jakeyoshimoto/emg-robot-arm/CAD/v6/Index mcp v6.STL

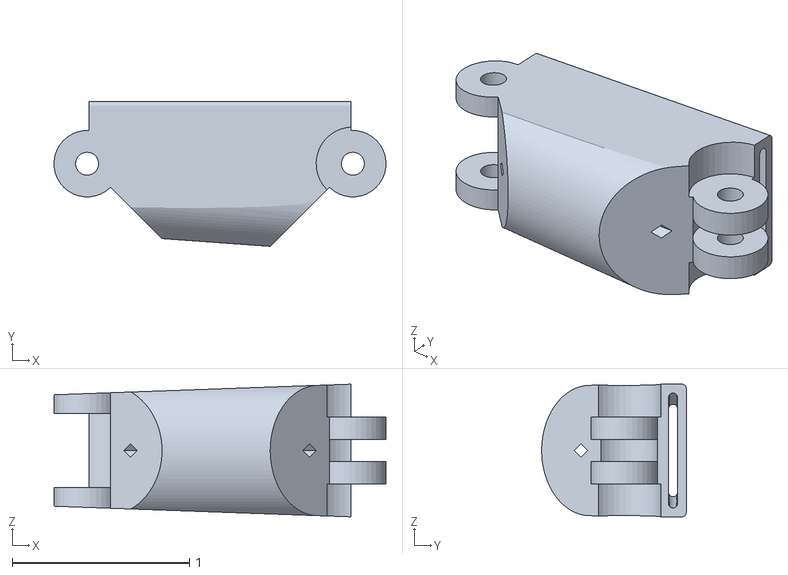
[picture p15: CAD file, 2026-07-24]
CAD/v6/Index mcp v6.STL
1.87 x 0.817 x 0.749
