jakeyoshimoto/emg-robot-arm/CAD/6DoF Arm/Arm 1.stl

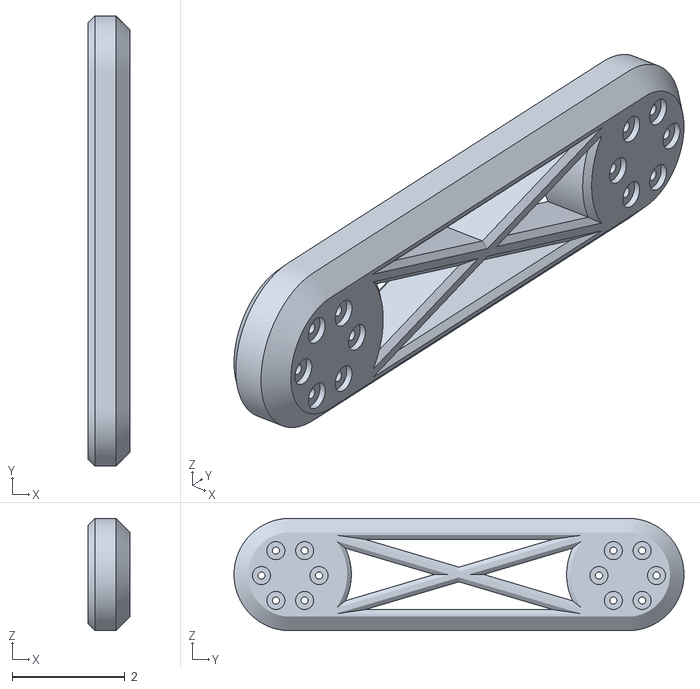
[picture p16: CAD file, 2026-07-29]
CAD/6DoF Arm/Arm 1.stl
0.75 x 8.00 x 2.00
