jakeyoshimoto/emg-robot-arm/CAD/Cycloidal Drive Gearbox/CDG V2 - Bottom Plate.stl

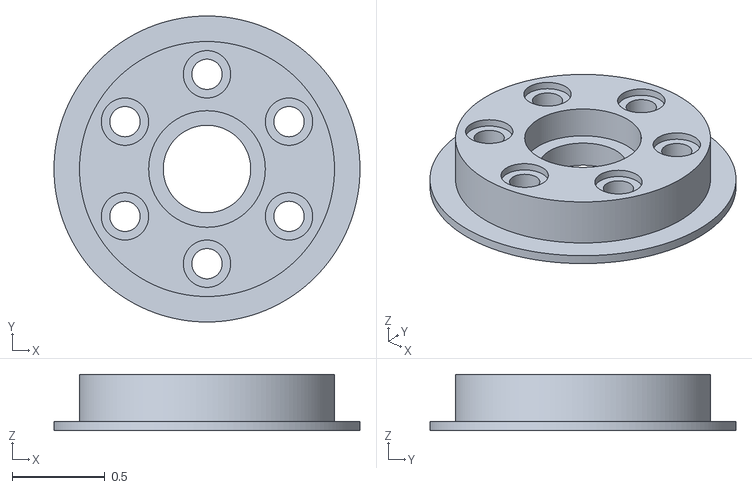
[picture p17: CAD file, 2026-07-28]
CAD/Cycloidal Drive Gearbox/CDG V2 - Bottom Plate.stl
1.65 x 1.65 x 0.305
