jakeyoshimoto/emg-robot-arm/CAD/v6/Middle_Ring dip v6.STL

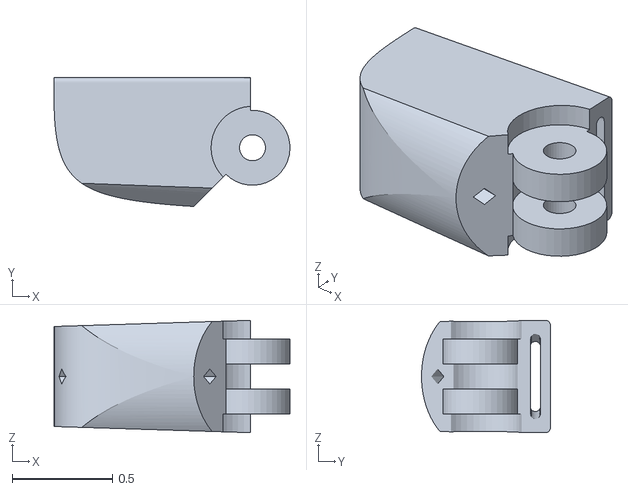
[picture p18: CAD file, 2026-07-24]
CAD/v6/Middle_Ring dip v6.STL
1.18 x 0.645 x 0.562
