jakeyoshimoto/emg-robot-arm/CAD/6DoF Arm/Arm 2.stl

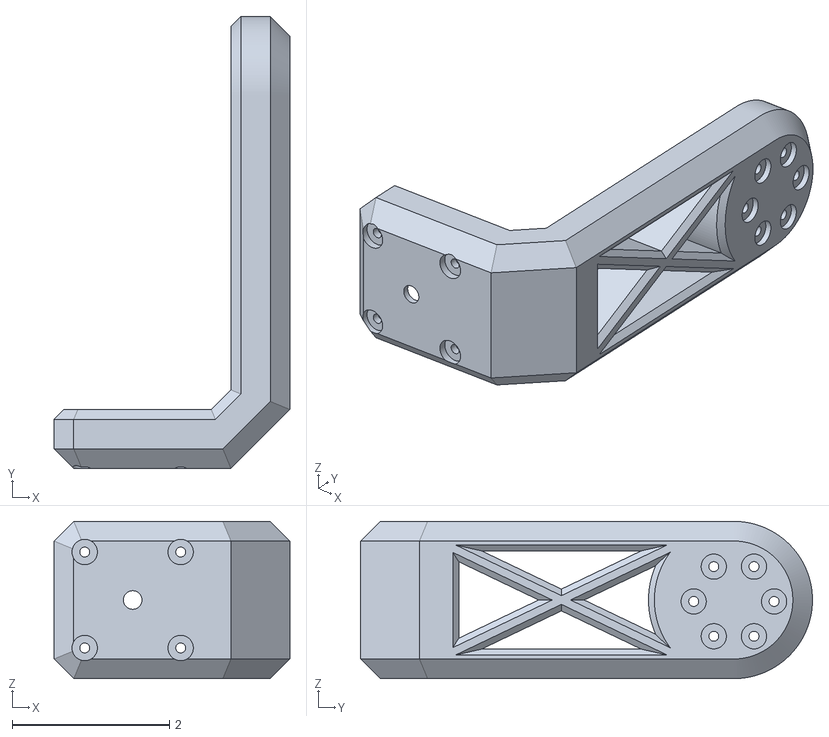
[picture p19: CAD file, 2026-07-29]
CAD/6DoF Arm/Arm 2.stl
3.00 x 5.75 x 2.00
