jakeyoshimoto/emg-robot-arm/CAD/v6/Middle_Ring pip v6.STL

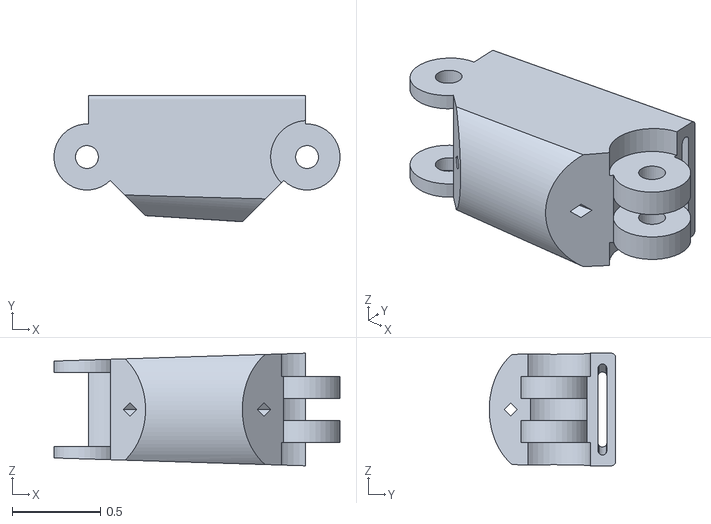
[picture p20: CAD file, 2026-07-24]
CAD/v6/Middle_Ring pip v6.STL
1.62 x 0.718 x 0.64
