jakeyoshimoto/emg-robot-arm/CAD/Cycloidal Drive Gearbox/CDG V2 - Top Plate.stl

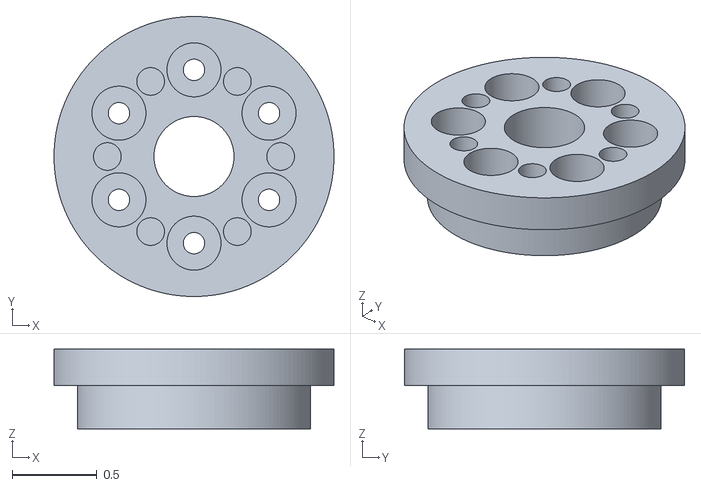
[picture p21: CAD file, 2026-07-28]
CAD/Cycloidal Drive Gearbox/CDG V2 - Top Plate.stl
1.65 x 1.65 x 0.472
