jakeyoshimoto/emg-robot-arm/CAD/v6/palm top no thumb v7.STL

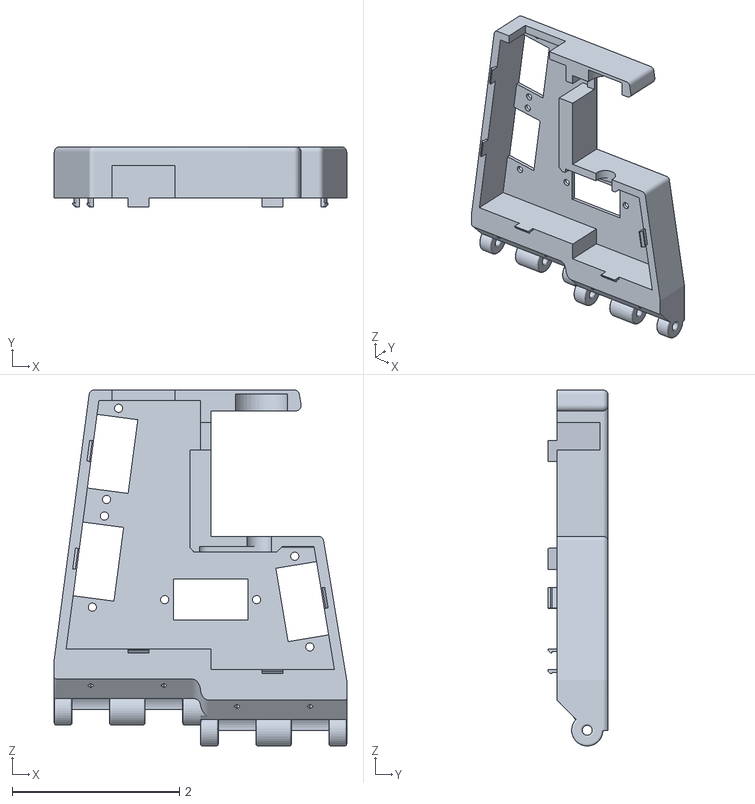
[picture p22: CAD file, 2026-07-24]
CAD/v6/palm top no thumb v7.STL
3.50 x 0.722 x 4.26
