jakeyoshimoto/emg-robot-arm/CAD/6DoF Arm/Hand Joint Mount.stl

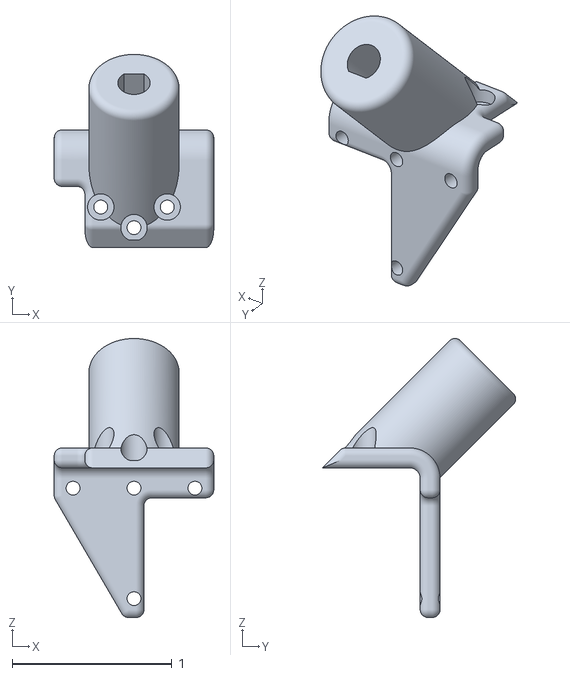
[picture p23: CAD file, 2026-07-29]
CAD/6DoF Arm/Hand Joint Mount.stl
1.00 x 1.21 x 1.75
