jakeyoshimoto/emg-robot-arm/CAD/Cycloidal Drive Gearbox/CDG V2 - Input Shaft T.stl

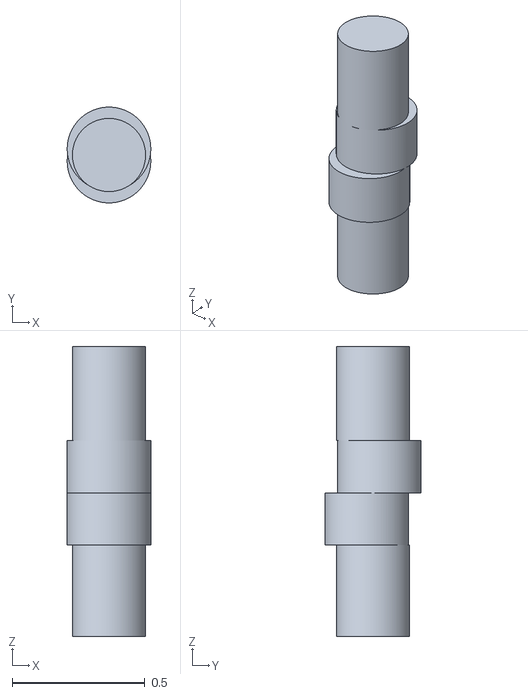
[picture p24: CAD file, 2026-07-28]
CAD/Cycloidal Drive Gearbox/CDG V2 - Input Shaft T.stl
0.315 x 0.361 x 1.09
