jakeyoshimoto/emg-robot-arm/CAD/v6/Pinky dip v6.STL

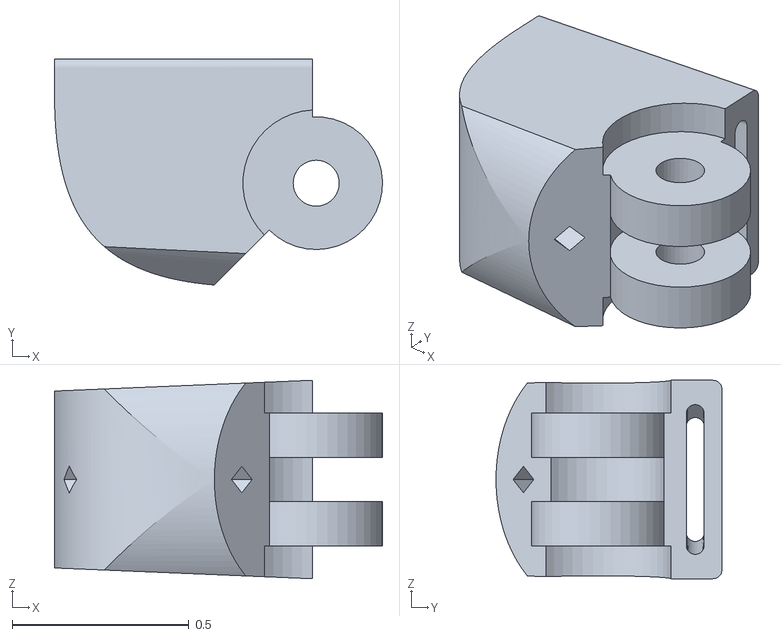
[picture p25: CAD file, 2026-07-24]
CAD/v6/Pinky dip v6.STL
0.927 x 0.639 x 0.561
