jakeyoshimoto/emg-robot-arm/CAD/v6/palm thumb v6.stl

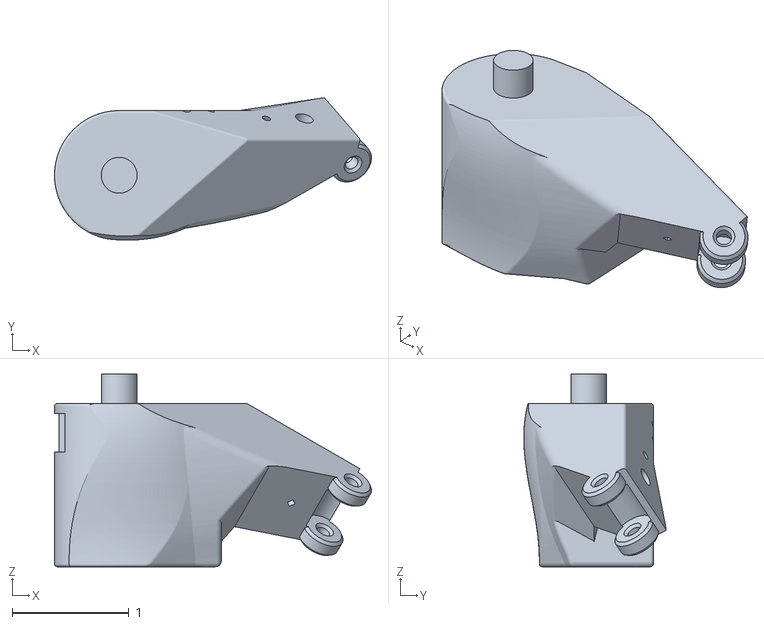
[picture p26: CAD file, 2026-07-24]
CAD/v6/palm thumb v6.stl
2.72 x 1.22 x 1.65
