jakeyoshimoto/emg-robot-arm/CAD/v6/Index pip v6.STL

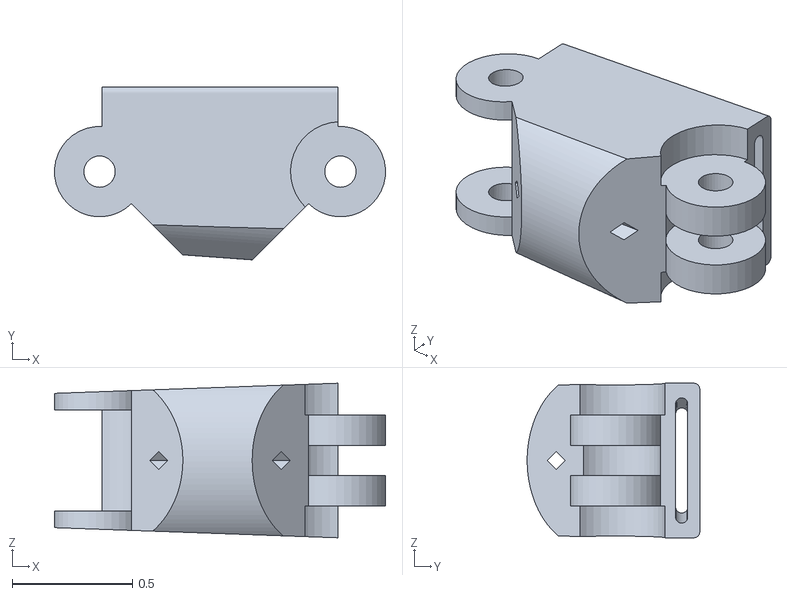
[picture p27: CAD file, 2026-07-24]
CAD/v6/Index pip v6.STL
1.37 x 0.717 x 0.642
