jakeyoshimoto/emg-robot-arm/CAD/v6/palm bot no thumb v7.STL

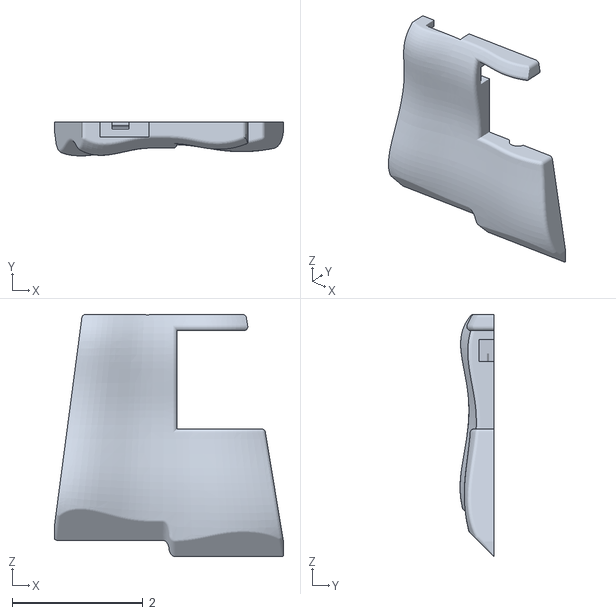
[picture p28: CAD file, 2026-07-24]
CAD/v6/palm bot no thumb v7.STL
3.50 x 0.519 x 3.70
