jakeyoshimoto/emg-robot-arm/CAD/v6/Index dip v6.STL

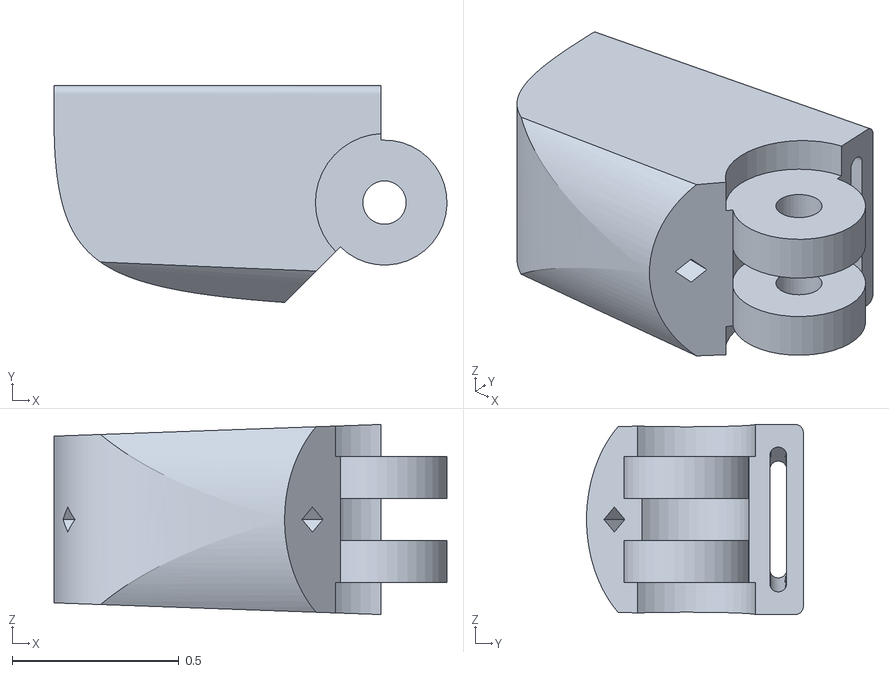
[picture p29: CAD file, 2026-07-24]
CAD/v6/Index dip v6.STL
1.18 x 0.651 x 0.57
