jakeyoshimoto/emg-robot-arm/CAD/v6/Middle_Ring mcp v6.STL

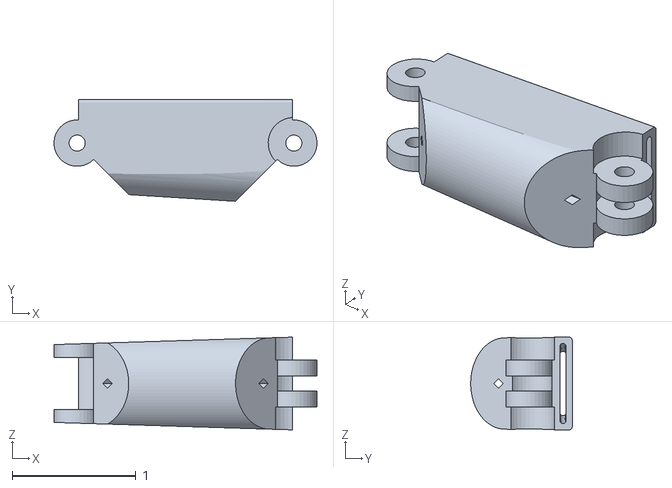
[picture p30: CAD file, 2026-07-24]
CAD/v6/Middle_Ring mcp v6.STL
2.12 x 0.821 x 0.749
