jakeyoshimoto/emg-robot-arm/CAD/v6/Pinky mcp v6.STL

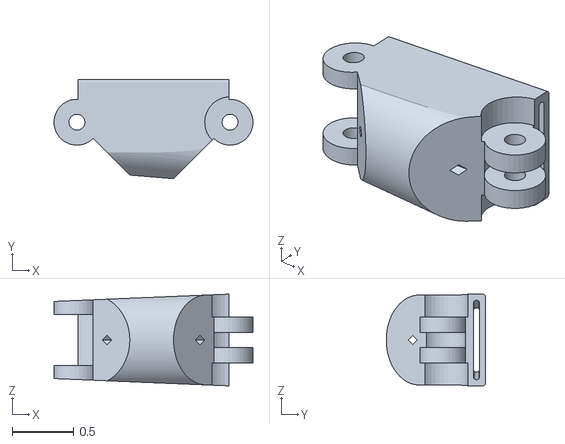
[picture p31: CAD file, 2026-07-24]
CAD/v6/Pinky mcp v6.STL
1.62 x 0.812 x 0.749
